vvigilante/comelit-simplebus1/web_intercom/cert.h

#ifndef CERT_H_
#define CERT_H_
unsigned char example_crt_DER[] = {
  0x30, 0x82, 0x02, 0x64, 0x30, 0x82, 0x01, 0xcd, 0xa0, 0x03, 0x02, 0x01,
  0x02, 0x02, 0x01, 0x07, 0x30, 0x0d, 0x06, 0x09, 0x2a, 0x86, 0x48, 0x86,
  0xf7, 0x0d, 0x01, 0x01, 0x0b, 0x05, 0x00, 0x30, 0x56, 0x31, 0x0b, 0x30,
  0x09, 0x06, 0x03, 0x55, 0x04, 0x06, 0x13, 0x02, 0x49, 0x54, 0x31, 0x0b,
  0x30, 0x09, 0x06, 0x03, 0x55, 0x04, 0x08, 0x0c, 0x02, 0x53, 0x41, 0x31,
  0x10, 0x30, 0x0e, 0x06, 0x03, 0x55, 0x04, 0x07, 0x0c, 0x07, 0x53, 0x61,
  0x6c, 0x65, 0x72, 0x6e, 0x6f, 0x31, 0x13, 0x30, 0x11, 0x06, 0x03, 0x55,
  0x04, 0x0a, 0x0c, 0x0a, 0x76, 0x76, 0x69, 0x67, 0x69, 0x6c, 0x61, 0x6e,
  0x74, 0x65, 0x31, 0x13, 0x30, 0x11, 0x06, 0x03, 0x55, 0x04, 0x03, 0x0c,
  0x0a, 0x6d, 0x79, 0x63, 0x61, 0x2e, 0x6c, 0x6f, 0x63, 0x61, 0x6c, 0x30,
  0x1e, 0x17, 0x0d, 0x32, 0x31, 0x30, 0x34, 0x30, 0x31, 0x30, 0x39, 0x33,
  0x30, 0x31, 0x33, 0x5a, 0x17, 0x0d, 0x33, 0x31, 0x30, 0x33, 0x33, 0x30,
  0x30, 0x39, 0x33, 0x30, 0x31, 0x33, 0x5a, 0x30, 0x5a, 0x31, 0x0b, 0x30,
  0x09, 0x06, 0x03, 0x55, 0x04, 0x06, 0x13, 0x02, 0x49, 0x54, 0x31, 0x0b,
  0x30, 0x09, 0x06, 0x03, 0x55, 0x04, 0x08, 0x0c, 0x02, 0x53, 0x41, 0x31,
  0x10, 0x30, 0x0e, 0x06, 0x03, 0x55, 0x04, 0x07, 0x0c, 0x07, 0x53, 0x61,
  0x6c, 0x65, 0x72, 0x6e, 0x6f, 0x31, 0x13, 0x30, 0x11, 0x06, 0x03, 0x55,
  0x04, 0x0a, 0x0c, 0x0a, 0x76, 0x76, 0x69, 0x67, 0x69, 0x6c, 0x61, 0x6e,
  0x74, 0x65, 0x31, 0x17, 0x30, 0x15, 0x06, 0x03, 0x55, 0x04, 0x03, 0x0c,
  0x0e, 0x69, 0x6e, 0x74, 0x65, 0x72, 0x63, 0x6f, 0x6d, 0x2e, 0x6c, 0x6f,
  0x63, 0x61, 0x6c, 0x30, 0x81, 0x9f, 0x30, 0x0d, 0x06, 0x09, 0x2a, 0x86,
  0x48, 0x86, 0xf7, 0x0d, 0x01, 0x01, 0x01, 0x05, 0x00, 0x03, 0x81, 0x8d,
  0x00, 0x30, 0x81, 0x89, 0x02, 0x81, 0x81, 0x00, 0xbd, 0x1b, 0xa5, 0x16,
  0x8b, 0xd7, 0xe3, 0xa1, 0xf6, 0xb8, 0xa8, 0xf2, 0xfc, 0x53, 0x2e, 0x4b,
  0x9f, 0xfb, 0x71, 0xf8, 0x2c, 0x9a, 0xc4, 0x02, 0x99, 0x0d, 0x4e, 0xdd,
  0x29, 0x04, 0x7c, 0xa0, 0xe6, 0x00, 0x20, 0x0f, 0x5a, 0x5a, 0x96, 0x10,
  0xf7, 0x91, 0x5b, 0xf6, 0xae, 0x2e, 0x48, 0x3e, 0x8b, 0x02, 0xba, 0x35,
  0x5e, 0x0a, 0xbf, 0x39, 0x78, 0xe5, 0x58, 0x92, 0xe9, 0xe0, 0x33, 0x1a,
  0x9a, 0x9c, 0xf1, 0x05, 0x5e, 0xc0, 0x9f, 0x90, 0xb6, 0x0d, 0x27, 0x6b,
  0x86, 0xf9, 0x24, 0xb3, 0x7c, 0x93, 0xbc, 0xdb, 0x1c, 0xbf, 0xb6, 0xd2,
  0x33, 0xc3, 0x8d, 0x97, 0x8b, 0x1b, 0xa6, 0x18, 0x36, 0x18, 0x9c, 0xc8,
  0x7b, 0xf3, 0x32, 0xdb, 0x67, 0x53, 0xc2, 0x21, 0x81, 0xee, 0xc1, 0x9e,
  0xe8, 0xd9, 0x82, 0xd1, 0x28, 0xfe, 0xfb, 0x0b, 0x4c, 0xde, 0x31, 0xc3,
  0x0c, 0xe2, 0xdf, 0xf3, 0x02, 0x03, 0x01, 0x00, 0x01, 0xa3, 0x3e, 0x30,
  0x3c, 0x30, 0x3a, 0x06, 0x03, 0x55, 0x1d, 0x11, 0x04, 0x33, 0x30, 0x31,
  0x82, 0x12, 0x77, 0x77, 0x77, 0x2e, 0x69, 0x6e, 0x74, 0x65, 0x72, 0x63,
  0x6f, 0x6d, 0x2e, 0x6c, 0x6f, 0x63, 0x61, 0x6c, 0x82, 0x0e, 0x69, 0x6e,
  0x74, 0x65, 0x72, 0x63, 0x6f, 0x6d, 0x2e, 0x6c, 0x6f, 0x63, 0x61, 0x6c,
  0x82, 0x0b, 0x31, 0x30, 0x2e, 0x31, 0x30, 0x2e, 0x31, 0x30, 0x2e, 0x31,
  0x35, 0x30, 0x0d, 0x06, 0x09, 0x2a, 0x86, 0x48, 0x86, 0xf7, 0x0d, 0x01,
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
};
unsigned int example_crt_DER_len = 616;
#endif
