vvigilante/comelit-simplebus1/web_intercom/private_key.h

#ifndef PRIVATE_KEY_H_
#define PRIVATE_KEY_H_
unsigned char example_key_DER[] = {
  0x30, 0x82, 0x02, 0x5c, 0x02, 0x01, 0x00, 0x02, 0x81, 0x81, 0x00, 0xbd,
  0x1b, 0xa5, 0x16, 0x8b, 0xd7, 0xe3, 0xa1, 0xf6, 0xb8, 0xa8, 0xf2, 0xfc,
  0x53, 0x2e, 0x4b, 0x9f, 0xfb, 0x71, 0xf8, 0x2c, 0x9a, 0xc4, 0x02, 0x99,
  0x0d, 0x4e, 0xdd, 0x29, 0x04, 0x7c, 0xa0, 0xe6, 0x00, 0x20, 0x0f, 0x5a,
  0x5a, 0x96, 0x10, 0xf7, 0x91, 0x5b, 0xf6, 0xae, 0x2e, 0x48, 0x3e, 0x8b,
  0x02, 0xba, 0x35, 0x5e, 0x0a, 0xbf, 0x39, 0x78, 0xe5, 0x58, 0x92, 0xe9,
  0xe0, 0x33, 0x1a, 0x9a, 0x9c, 0xf1, 0x05, 0x5e, 0xc0, 0x9f, 0x90, 0xb6,
  0x0d, 0x27, 0x6b, 0x86, 0xf9, 0x24, 0xb3, 0x7c, 0x93, 0xbc, 0xdb, 0x1c,
  0xbf, 0xb6, 0xd2, 0x33, 0xc3, 0x8d, 0x97, 0x8b, 0x1b, 0xa6, 0x18, 0x36,
  0x18, 0x9c, 0xc8, 0x7b, 0xf3, 0x32, 0xdb, 0x67, 0x53, 0xc2, 0x21, 0x81,
  0xee, 0xc1, 0x9e, 0xe8, 0xd9, 0x82, 0xd1, 0x28, 0xfe, 0xfb, 0x0b, 0x4c,
  0xde, 0x31, 0xc3, 0x0c, 0xe2, 0xdf, 0xf3, 0x02, 0x03, 0x01, 0x00, 0x01,
  0x02, 0x81, 0x81, 0x00, 0xa7, 0x53, 0xff, 0xc6, 0xac, 0x64, 0x91, 0xb9,
  0xad, 0x3a, 0x85, 0xdb, 0xc3, 0x22, 0xc2, 0xf3, 0x0d, 0x93, 0x0a, 0xac,
  0x42, 0xa3, 0x8a, 0xce, 0x95, 0xa8, 0xad, 0xe0, 0x89, 0x3b, 0xbc, 0x1f,
  0x0e, 0x84, 0x8b, 0xd9, 0xa9, 0xe4, 0x3f, 0xa6, 0xb1, 0xb8, 0x3f, 0xfc,
  0x4c, 0xf1, 0x0c, 0xe1, 0xb2, 0x54, 0xee, 0x78, 0xec, 0x46, 0x6c, 0x1f,
  0xa9, 0x76, 0x9d, 0xe2, 0x18, 0xe9, 0x55, 0xad, 0x2e, 0x40, 0xba, 0xa8,
  0x2f, 0xf9, 0x18, 0x3e, 0xa1, 0x3f, 0x6a, 0x67, 0x21, 0x1d, 0x7e, 0xe4,
  0x4a, 0x99, 0x18, 0xce, 0xdf, 0x11, 0x13, 0x23, 0x91, 0x0f, 0x48, 0xc7,
  0x73, 0x8b, 0xb8, 0x8a, 0x08, 0xea, 0xb6, 0x6b, 0x4a, 0x1e, 0xe5, 0x27,
  0xdf, 0xd8, 0x21, 0xfc, 0x99, 0x56, 0x8f, 0xd3, 0xe4, 0xad, 0x3a, 0xb9,
  0xe1, 0xb9, 0x33, 0xf8, 0xc2, 0xa0, 0x99, 0xb6, 0xaa, 0x92, 0xce, 0x41,
  0x02, 0x41, 0x00, 0xdd, 0x8d, 0xa3, 0xd4, 0x6f, 0x4f, 0x9d, 0x8c, 0x1f,
  0xf3, 0x90, 0xe1, 0x13, 0xb3, 0xe3, 0x36, 0xed, 0xb8, 0xad, 0x89, 0x78,
  0xdd, 0x8a, 0x75, 0xc0, 0xd4, 0x13, 0x3b, 0x9e, 0x70, 0x04, 0x5c, 0xf7,
  0x36, 0x64, 0x1f, 0xb4, 0x6e, 0x45, 0x44, 0x66, 0xc9, 0xc9, 0x7d, 0xdd,
  0x9c, 0xe3, 0xae, 0xc6, 0x2b, 0x2f, 0xba, 0x7e, 0x57, 0xf2, 0xe7, 0xf0,
  0x07, 0x4f, 0x58, 0xa0, 0x51, 0xff, 0x13, 0x02, 0x41, 0x00, 0xda, 0x82,
  0x9a, 0x6e, 0x0d, 0x97, 0x94, 0xfb, 0x6f, 0xe1, 0xde, 0x3d, 0xa7, 0xce,
  0x68, 0xd5, 0xc8, 0xcc, 0xe8, 0xbe, 0x77, 0x3d, 0x12, 0xf3, 0xbc, 0xca,
  0xfa, 0x7f, 0xd2, 0xa5, 0x3a, 0xec, 0xb2, 0x41, 0xb9, 0xd8, 0x38, 0x94,
  0xdf, 0x5c, 0xcd, 0xd5, 0x1d, 0x08, 0xdd, 0x0e, 0x50, 0x44, 0x20, 0x41,
  0xbc, 0x72, 0x97, 0x29, 0x58, 0x1d, 0x1e, 0x23, 0x05, 0xa5, 0xd0, 0x16,
  0x57, 0xa1, 0x02, 0x40, 0x70, 0xb2, 0xd1, 0x08, 0x89, 0xca, 0xac, 0xf0,
  0x8f, 0x7c, 0x3d, 0x51, 0x50, 0xcd, 0x6b, 0xa2, 0x10, 0x50, 0xa5, 0xed,
  0xcd, 0x0e, 0x9c, 0x95, 0x03, 0x8e, 0x9d, 0x6d, 0xf1, 0x4d, 0x37, 0xda,
  0xf6, 0x61, 0xb3, 0x92, 0xb1, 0x1c, 0x7a, 0x9d, 0xad, 0xcf, 0xad, 0x70,
  0x1a, 0x1f, 0xe9, 0x6d, 0x89, 0x1e, 0x84, 0xbb, 0xcf, 0xf2, 0xfa, 0xfb,
  0xe2, 0x8c, 0x45, 0x5f, 0x66, 0xc5, 0xef, 0x03, 0x02, 0x40, 0x6f, 0x51,
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
};
unsigned int example_key_DER_len = 608;
#endif
