vvigilante/comelit-simplebus1/libsimplebus/src/Logger.h

#include <stdlib.h>
#include <stdio.h>
#include <stdarg.h>
#include <Arduino.h>

#ifndef LOGGER_H_
#define LOGGER_H_

#define MAX(a,b) ((a)>(b)?(a):(b))


/**
 * A buffered logger abstract class that allows for different implementations.
 * Initialize the concrete logger and assign it to the global "logger" variable.
 * The rest of the program just needs to call the "LOG" macro
 */
class Logger
{
public:
    Logger(size_t buf_size){
        this->buffer = (char*)malloc(buf_size);
        this->pos = 0;
        this->buf_size = buf_size;
    }

   void log(bool wnewline, const char* format, ...)
   {
        // use x, y and b
        const char* b = this->buffer+this->pos;
        va_list argptr;
        va_start(argptr, format);
        size_t n;
        if(wnewline){
            unsigned long time = millis();
            n = snprintf(this->buffer+this->pos, MAX(0, this->buf_size-this->pos-2), "%d.%03d - ", time/1000, time%1000);
            this->pos += n;
        }
        n = vsnprintf(this->buffer+this->pos, MAX(0, this->buf_size-this->pos-2), format, argptr);
        this->pos += n;
        if(wnewline && this->pos<this->buf_size-1)
            this->buffer[this->pos++]='\n';
        this->buffer[this->pos]='\0';
        va_end(argptr);
        this->flush();
   }
   virtual void flush(bool force = false) = 0;

protected:
   char* buffer;
   size_t pos;
   size_t buf_size;
};

extern Logger* logger;

#define LOG(...) do{ if(logger) logger->log(true, __VA_ARGS__); }while(0)

#endif /* LOGGER_H_ */
